devices-lab/solderbit-gamepad/media/version-images/solderbit-gamepad-v0.2.png

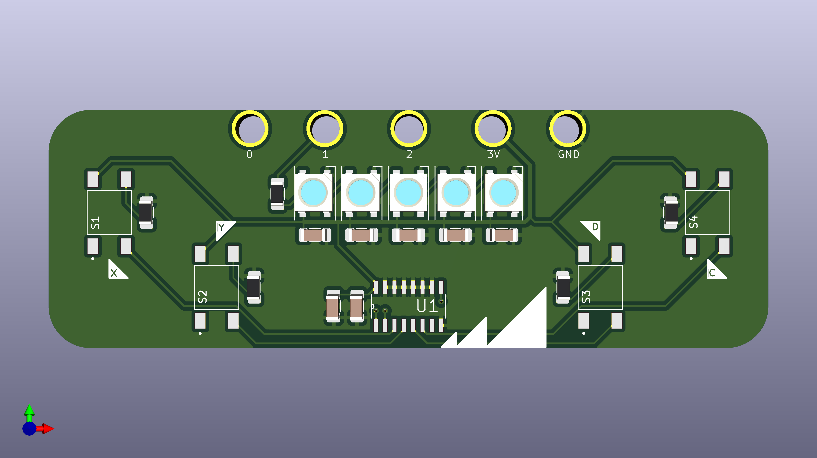
media/version-images/solderbit-gamepad-v0.2.png
