devices-lab/solderbit-gamepad/media/version-images/solderbit-gamepad-v0.4.png

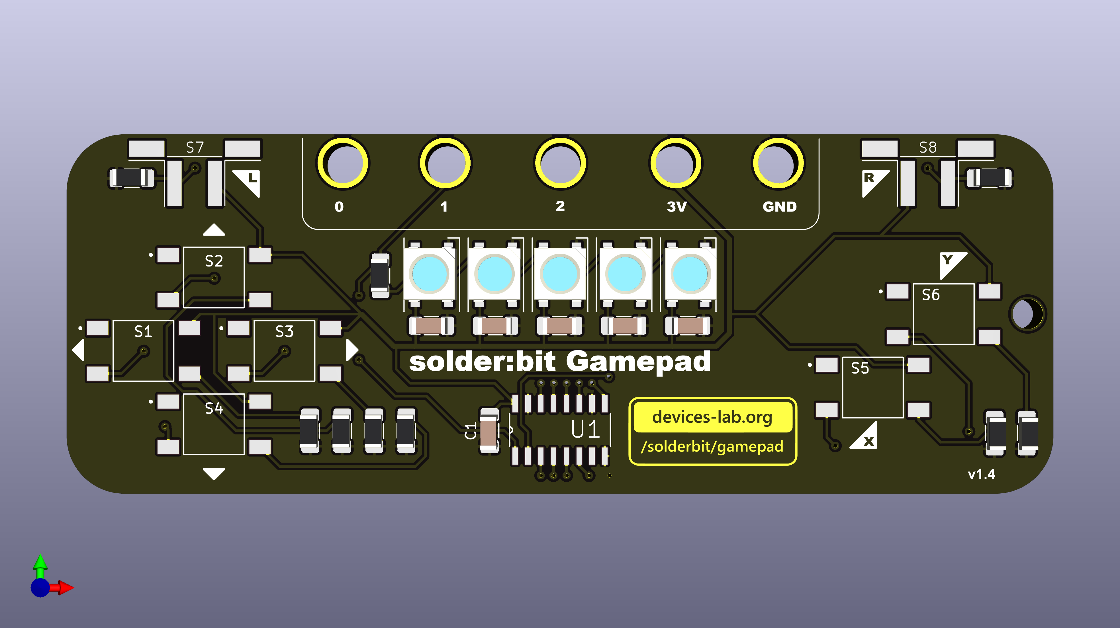
media/version-images/solderbit-gamepad-v0.4.png
