devices-lab/solderbit-gamepad/media/version-images/solderbit-gamepad-v0.7.png

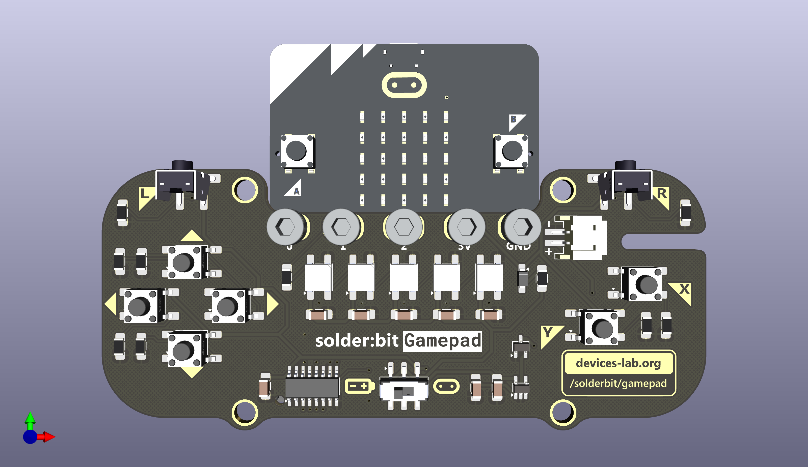
media/version-images/solderbit-gamepad-v0.7.png
